tomasmcguinness/matter-nrf-dual-temperature-sensor/firmware/src/app_task.h

/*
 * Copyright (c) 2021 Nordic Semiconductor ASA
 *
 * SPDX-License-Identifier: LicenseRef-Nordic-5-Clause
 */

#pragma once

#include <platform/CHIPDeviceLayer.h>

using namespace ::chip::DeviceLayer;

struct Identify;

class AppTask
{
public:
	static AppTask &Instance()
	{
		static AppTask sAppTask;
		return sAppTask;
	};

	CHIP_ERROR StartApp();

	static void IdentifyStartHandler(Identify *);
	static void IdentifyStopHandler(Identify *);

private:
	CHIP_ERROR Init();

	static void MatterEventHandler(const ChipDeviceEvent *event, intptr_t data);
	static void SensorMeasureHandler();
	static void SensorTimerCallback(k_timer *timer);
	static void BatteryMeasureHandler();
	static void BatteryTimerCallback(k_timer *timer);
	static void IndicatorTimerCallback(k_timer *timer);
	static void FactoryResetTimerCallback(k_timer *timer);
	static void FactoryResetHandler();
#ifdef CONFIG_CHIP_ICD_UAT_SUPPORT
	static void UserActiveModeHandler();
#endif

	static void ResetButtonCallback(const struct device *dev, struct gpio_callback *cb, uint32_t pins);
	static void ButtonDebounceTimerCallback(k_timer *timer);
	static void ResetButtonHandler();

	void ConfigureGPIO();
};
